Tejas2910/Solder-Reflow-Hot-Plate/EDL_Codes/ST7735.h

/***************************************************
  This is a library for the Adafruit 1.8" SPI display.
This library works with the Adafruit 1.8" TFT Breakout w/SD card
  ----> http://www.adafruit.com/products/358
The 1.8" TFT shield
  ----> https://www.adafruit.com/product/802
The 1.44" TFT breakout
  ----> https://www.adafruit.com/product/2088
as well as Adafruit raw 1.8" TFT display
  ----> http://www.adafruit.com/products/618
  Check out the links above for our tutorials and wiring diagrams
  These displays use SPI to communicate, 4 or 5 pins are required to
  interface (RST is optional)
  Adafruit invests time and resources providing this open source code,
  please support Adafruit and open-source hardware by purchasing
  products from Adafruit!
  Written by Limor Fried/Ladyada for Adafruit Industries.
  MIT license, all text above must be included in any redistribution

  Ported to tm4c123gh6pm by Julian Fell.
 ****************************************************/

#ifndef _ADAFRUIT_ST7735H_
#define _ADAFRUIT_ST7735H_
#include "myLib.h"
//*****************************************************************************
//
// Screen commands
//
//*****************************************************************************

#define ST7735_NOP     0x00
#define ST7735_SWRESET 0x01
#define ST7735_RDDID   0x04
#define ST7735_RDDST   0x09

#define ST7735_SLPIN   0x10
#define ST7735_SLPOUT  0x11
#define ST7735_PTLON   0x12
#define ST7735_NORON   0x13

#define ST7735_INVOFF  0x20
#define ST7735_INVON   0x21
#define ST7735_DISPOFF 0x28
#define ST7735_DISPON  0x29
#define ST7735_CASET   0x2A
#define ST7735_RASET   0x2B
#define ST7735_RAMWR   0x2C
#define ST7735_RAMRD   0x2E

#define ST7735_PTLAR   0x30
#define ST7735_COLMOD  0x3A
#define ST7735_MADCTL  0x36

#define ST7735_FRMCTR1 0xB1
#define ST7735_FRMCTR2 0xB2
#define ST7735_FRMCTR3 0xB3
#define ST7735_INVCTR  0xB4
#define ST7735_DISSET5 0xB6

#define ST7735_PWCTR1  0xC0
#define ST7735_PWCTR2  0xC1
#define ST7735_PWCTR3  0xC2
#define ST7735_PWCTR4  0xC3
#define ST7735_PWCTR5  0xC4
#define ST7735_VMCTR1  0xC5

#define ST7735_RDID1   0xDA
#define ST7735_RDID2   0xDB
#define ST7735_RDID3   0xDC
#define ST7735_RDID4   0xDD

#define ST7735_PWCTR6  0xFC

#define ST7735_GMCTRP1 0xE0
#define ST7735_GMCTRN1 0xE1

#define MADCTL_MY  0x80
#define MADCTL_MX  0x40
#define MADCTL_MV  0x20
#define MADCTL_ML  0x10
#define MADCTL_RGB 0x00
#define MADCTL_BGR 0x08
#define MADCTL_MH  0x04

//*****************************************************************************
//
// Colour Definitions
//
//*****************************************************************************
#define	ST7735_BLACK   0x0000
#define	ST7735_RED     0x001F
#define	ST7735_BLUE    0xF800
#define	ST7735_GREEN   0x07E0
#define ST7735_CYAN    0x07FF
#define ST7735_MAGENTA 0xF81F
#define ST7735_YELLOW  0xFFE0  
#define ST7735_WHITE   0xFFFF

//*****************************************************************************
//
// Function Prototypes
//
//*****************************************************************************

void LcdInit(void);
void setAddrWindow(uint8_t x0, uint8_t y0, uint8_t x1, uint8_t y1);
void pushColor(uint16_t color);
void drawPixel(int16_t x, int16_t y, uint16_t color);
void drawFastVLine(int16_t x, int16_t y, int16_t h, uint16_t color);
void drawFastHLine(int16_t x, int16_t y, int16_t w, uint16_t color);
void fillScreen(uint16_t color);
void fillRect(int16_t x, int16_t y, int16_t w, int16_t h, uint16_t color);
uint16_t Color565(uint8_t r, uint8_t g, uint8_t b);
void setRotation(uint8_t m);
void invertDisplay(int8_t i);
void drawCircle(int16_t x0, int16_t y0, int16_t r, uint16_t colour);
void drawCircleHelper( int16_t x0, int16_t y0, int16_t r, uint8_t cornername, uint16_t colour);
void fillCircle(int16_t x0, int16_t y0, int16_t r, uint16_t colour);
void fillCircleHelper(int16_t x0, int16_t y0, int16_t r, uint8_t cornername, 
      int16_t delta, uint16_t colour);
void drawLine(int16_t x0, int16_t y0, int16_t x1, int16_t y1, uint16_t colour);
void drawRect(int16_t x, int16_t y, int16_t w, int16_t h, uint16_t colour);
void drawRoundRect(int16_t x, int16_t y, int16_t w, int16_t h, int16_t r, uint16_t colour);
void fillRoundRect(int16_t x, int16_t y, int16_t w, int16_t h, 
        int16_t r, uint16_t colour);
void drawTriangle(int16_t x0, int16_t y0, int16_t x1, int16_t y1,
        int16_t x2, int16_t y2, uint16_t colour);
void fillTriangle ( int16_t x0, int16_t y0, int16_t x1, int16_t y1,
          int16_t x2, int16_t y2, uint16_t colour);
void drawBitmap(int16_t x, int16_t y, const uint8_t *bitmap, int16_t w, int16_t h,
            uint16_t colour, uint16_t bg);
void drawXBitmap(int16_t x, int16_t y, const uint8_t *bitmap, 
            int16_t w, int16_t h, uint16_t colour);
void drawString(char *c, int16_t x, int16_t y, uint16_t colour, uint16_t bg, uint8_t size);
void drawNumber(int n, int16_t x, int16_t y, uint16_t colour, uint16_t bg, uint8_t size);
void drawChar(int16_t x, int16_t y, unsigned char c,
          uint16_t colour, uint16_t bg, uint8_t size);
void setCursor(int16_t x, int16_t y);
void setTextSize(uint8_t s);
void setTextColour(uint16_t c, uint16_t b);
void setTextWrap(uint16_t w);


static const unsigned char font[] = {
        0x00, 0x00, 0x00, 0x00, 0x00,   
  0x3E, 0x5B, 0x4F, 0x5B, 0x3E,   
  0x3E, 0x6B, 0x4F, 0x6B, 0x3E,   
  0x1C, 0x3E, 0x7C, 0x3E, 0x1C, 
  0x18, 0x3C, 0x7E, 0x3C, 0x18, 
  0x1C, 0x57, 0x7D, 0x57, 0x1C, 
  0x1C, 0x5E, 0x7F, 0x5E, 0x1C, 
  0x00, 0x18, 0x3C, 0x18, 0x00, 
  0xFF, 0xE7, 0xC3, 0xE7, 0xFF, 
  0x00, 0x18, 0x24, 0x18, 0x00, 
  0xFF, 0xE7, 0xDB, 0xE7, 0xFF, 
  0x30, 0x48, 0x3A, 0x06, 0x0E, 
  0x26, 0x29, 0x79, 0x29, 0x26, 
  0x40, 0x7F, 0x05, 0x05, 0x07, 
  0x40, 0x7F, 0x05, 0x25, 0x3F, 
  0x5A, 0x3C, 0xE7, 0x3C, 0x5A, 
  0x7F, 0x3E, 0x1C, 0x1C, 0x08, 
  0x08, 0x1C, 0x1C, 0x3E, 0x7F, 
  0x14, 0x22, 0x7F, 0x22, 0x14, 
  0x5F, 0x5F, 0x00, 0x5F, 0x5F, 
  0x06, 0x09, 0x7F, 0x01, 0x7F, 
  0x00, 0x66, 0x89, 0x95, 0x6A, 
  0x60, 0x60, 0x60, 0x60, 0x60, 
  0x94, 0xA2, 0xFF, 0xA2, 0x94, 
  0x08, 0x04, 0x7E, 0x04, 0x08, 
  0x10, 0x20, 0x7E, 0x20, 0x10, 
  0x08, 0x08, 0x2A, 0x1C, 0x08, 
  0x08, 0x1C, 0x2A, 0x08, 0x08, 
  0x1E, 0x10, 0x10, 0x10, 0x10, 
  0x0C, 0x1E, 0x0C, 0x1E, 0x0C, 
  0x30, 0x38, 0x3E, 0x38, 0x30, 
  0x06, 0x0E, 0x3E, 0x0E, 0x06, 
  0x00, 0x00, 0x00, 0x00, 0x00, 
  0x00, 0x00, 0x5F, 0x00, 0x00, 
  0x00, 0x07, 0x00, 0x07, 0x00, 
  0x14, 0x7F, 0x14, 0x7F, 0x14, 
  0x24, 0x2A, 0x7F, 0x2A, 0x12, 
  0x23, 0x13, 0x08, 0x64, 0x62, 
  0x36, 0x49, 0x56, 0x20, 0x50, 
  0x00, 0x08, 0x07, 0x03, 0x00, 
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
};

#endif
